intergalaktik/ulx4m-ld/pic/Blender_ULX4M-LD-003-full-ress.png

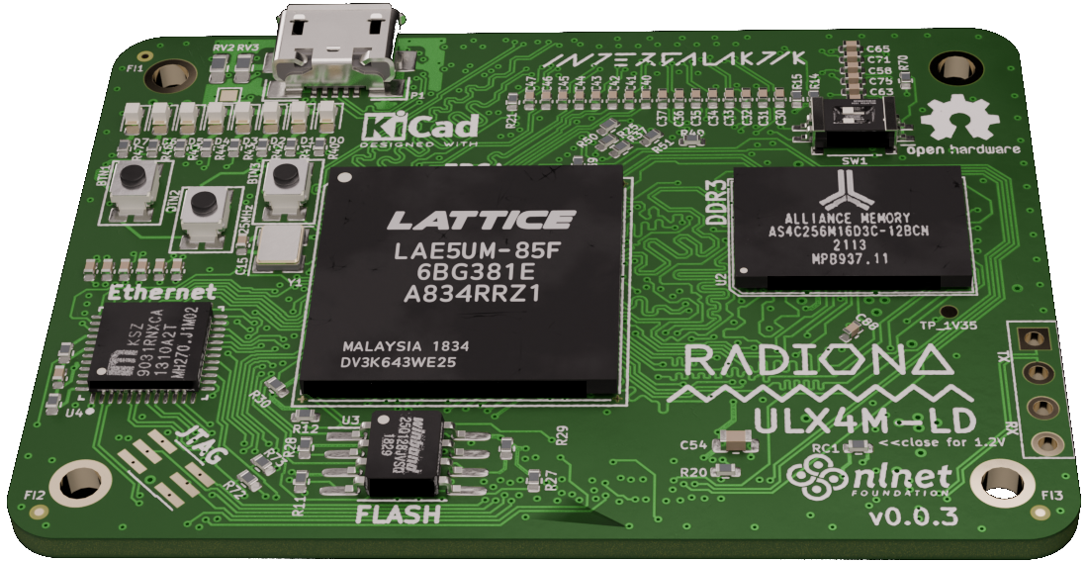
pic/Blender_ULX4M-LD-003-full-ress.png
