intergalaktik/ulx4m-ld/ddr3.kicad_sch

## KiCad design ddr3.kicad_sch (2025-04-05)

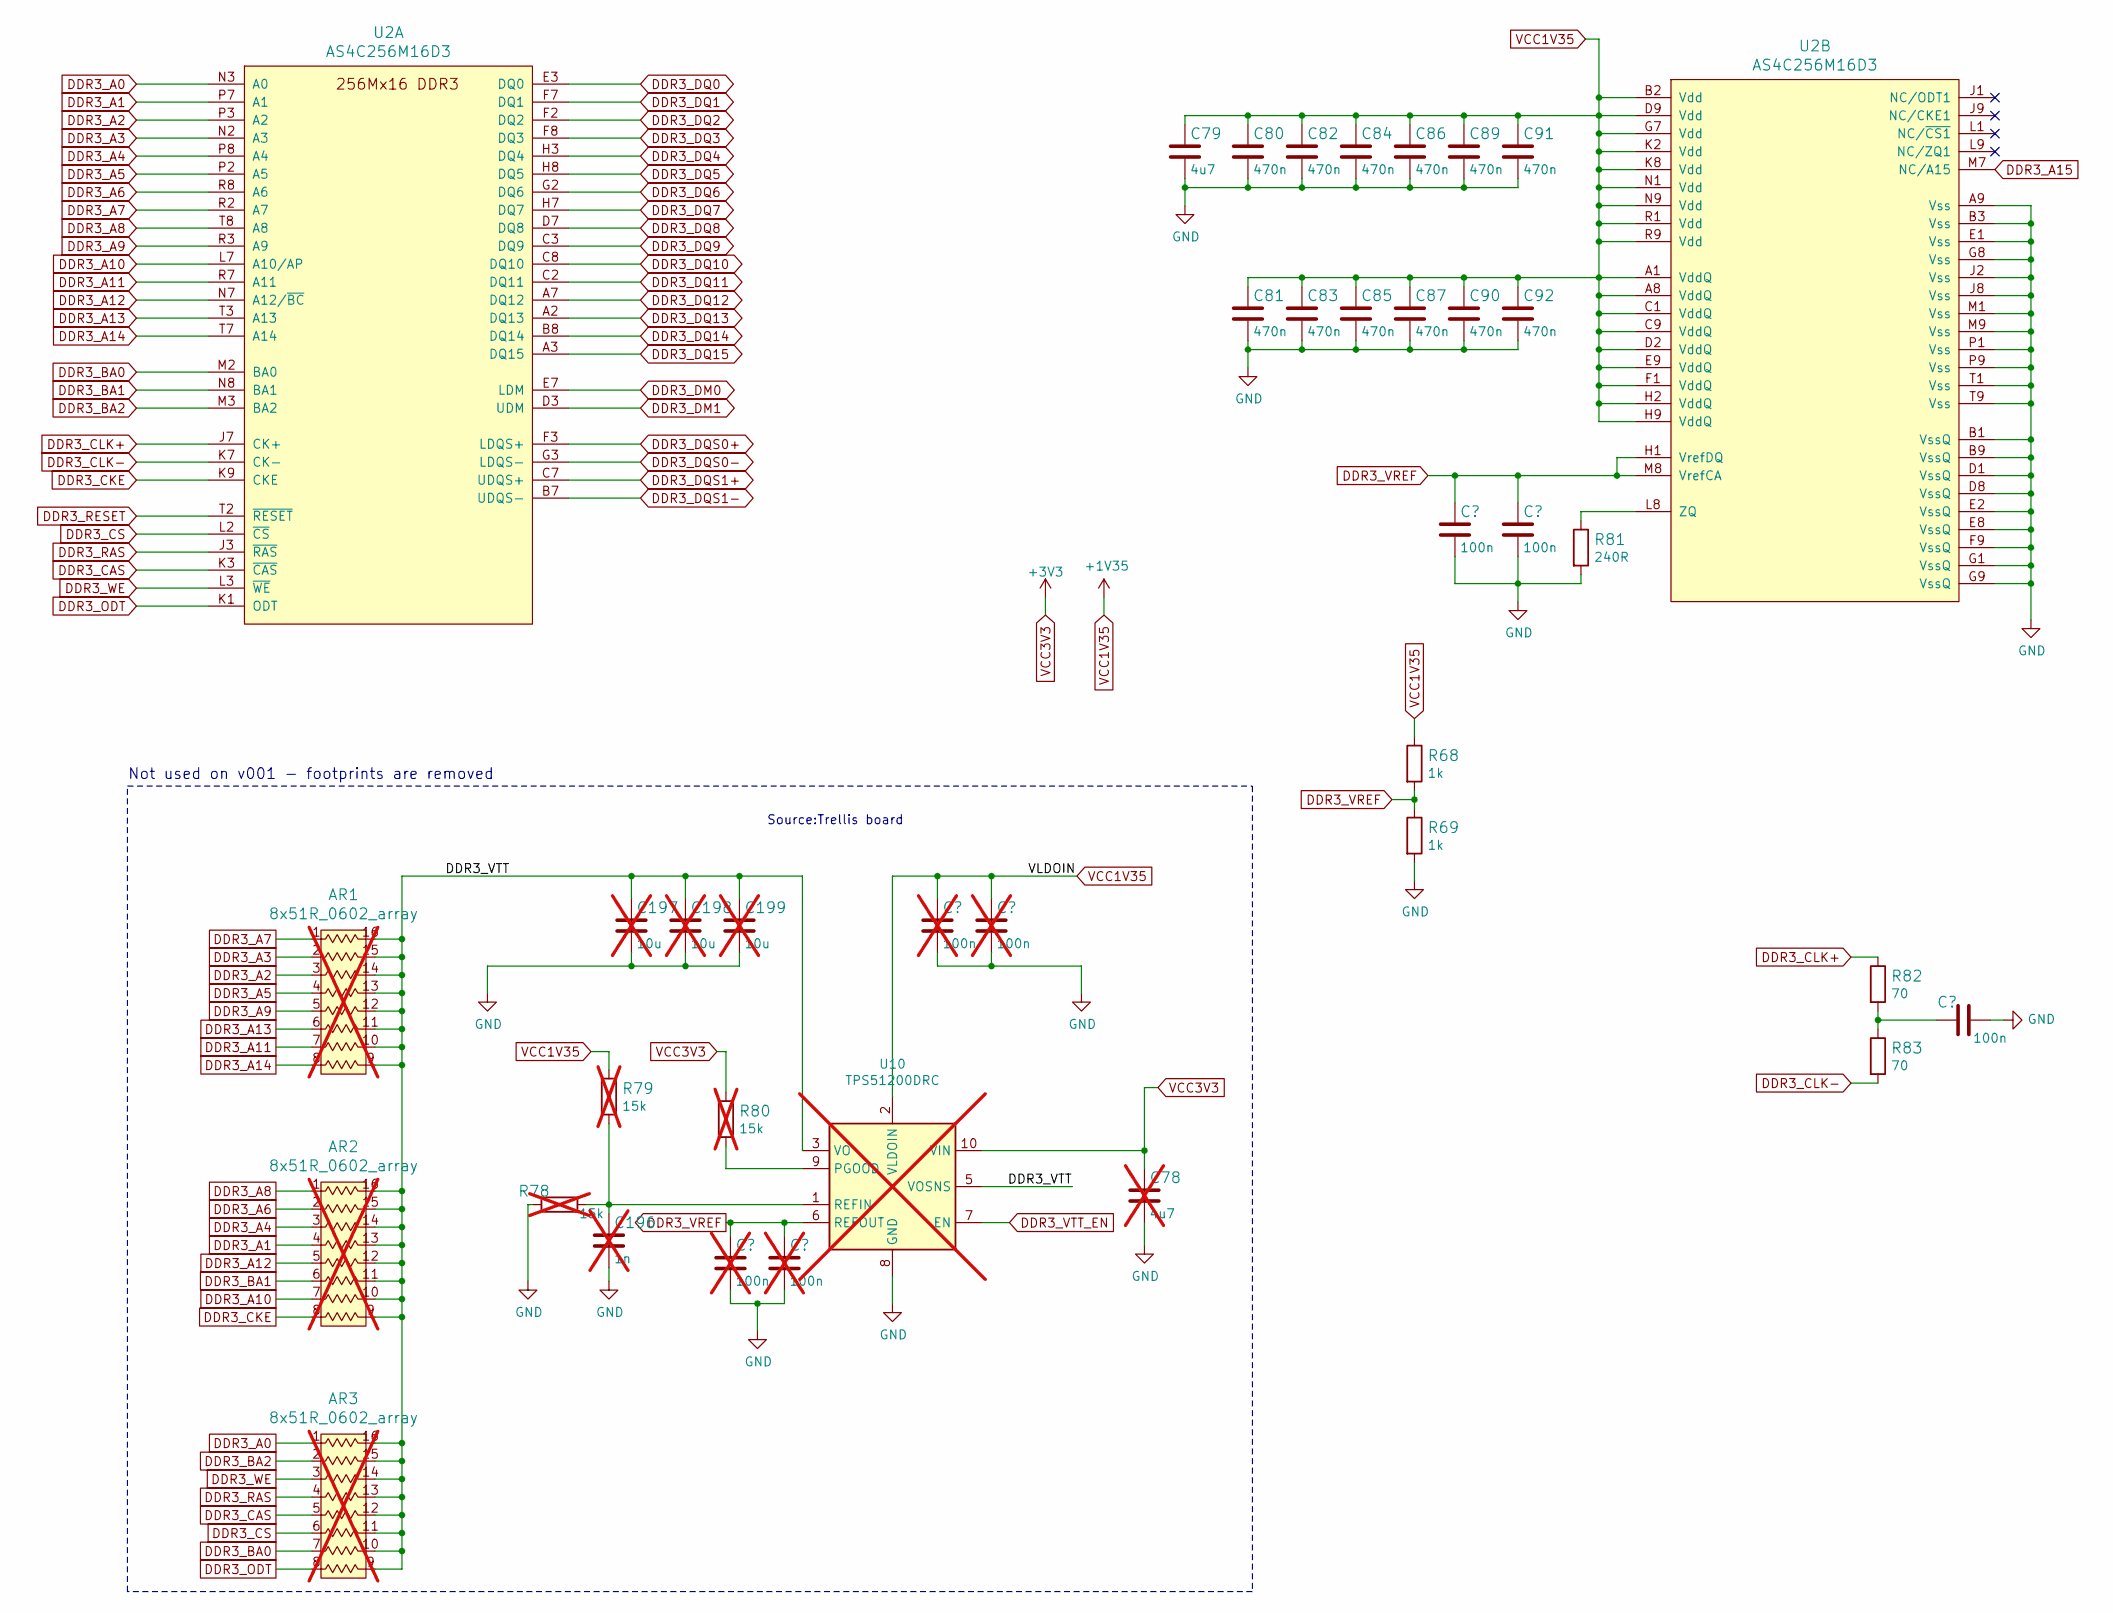
[picture p37: schematic ddr3.kicad_sch]

Parts:
AR1, AR2, AR3: 8x51R_0602_array; MPN EXB2HV510JV; not fitted
C78: 4u7; C_0402_1005Metric; MPN GRM155R60J106ME44D; not fitted
C79: 470n; C_0402_1005Metric; MPN GRM155R61A475MEAAD
C80, C81, C82, C83, C84, C85, C86, C87, C89, C90, C91, C92: 470n; C_0402_1005Metric; MPN C1005X5R1E474M050BB
C88, C93, C94: 100n; C_0402_1005Metric; MPN 0402X104K6R3CT
C196: 1n; MPN CC0402KRX7R9BB102; not fitted
C197, C198, C199: 10u; MPN GRM155R60J106ME44D; not fitted
C200, C201, C202, C240: 100n; MPN 0402X104K6R3CT; not fitted
R68, R69: 1k; R_0402_1005Metric; MPN CRCW040210K0FKEDHP
R78, R79, R80: 15k; MPN CRCW040210K0FKEDHP; not fitted
R81: 240R; R_0402_1005Metric; MPN ERJ2GEJ241X
R82, R83: 70; R_0402_1005Metric; MPN RC0402FR-0751RL
U2: AS4C256M16D3; BGA-96_9.0x13.0mm_Layout2x3x16_P0.8mm
U10: TPS51200DRC; not fitted

Connections:
+1V35: C79.1, C80.1, C81.1, C82.1, C83.1, C84.1, C85.1, C86.1, C87.1, C89.1, C90.1, C91.1, C92.1, C202.1, C240.1, R68.1, R79.1, U2.A1 (VddQ), U2.A8 (VddQ), U2.B2 (Vdd), U2.C1 (VddQ), U2.C9 (VddQ), U2.D2 (VddQ), U2.D9 (Vdd), U2.E9 (VddQ), U2.F1 (VddQ), U2.G7 (Vdd), U2.H2 (VddQ), U2.H9 (VddQ), U2.K2 (Vdd), U2.K8 (Vdd), U2.N1 (Vdd), U2.N9 (Vdd), U2.R1 (Vdd), U2.R9 (Vdd), U10.2 (VLDOIN)
+3V3: C78.1, R80.1, U10.10 (VIN)
DDR3_A0: AR3.1, U2.N3 (A0)
DDR3_A1: AR2.4, U2.P7 (A1)
DDR3_A2: AR1.3, U2.P3 (A2)
DDR3_A3: AR1.2, U2.N2 (A3)
DDR3_A4: AR2.3, U2.P8 (A4)
DDR3_A5: AR1.4, U2.P2 (A5)
DDR3_A6: AR2.2, U2.R8 (A6)
DDR3_A7: AR1.1, U2.R2 (A7)
DDR3_A8: AR2.1, U2.T8 (A8)
DDR3_A9: AR1.5, U2.R3 (A9)
DDR3_A10: AR2.7, U2.L7 (A10/AP)
DDR3_A11: AR1.7, U2.R7 (A11)
DDR3_A12: AR2.5, U2.N7 (A12/~BC)
DDR3_A13: AR1.6, U2.T3 (A13)
DDR3_A14: AR1.8, U2.T7 (A14)
DDR3_A15: U2.M7 (NC/A15)
DDR3_BA0: AR3.7, U2.M2 (BA0)
DDR3_BA1: AR2.6, U2.N8 (BA1)
DDR3_BA2: AR3.2, U2.M3 (BA2)
DDR3_CAS: AR3.5, U2.K3 (~CAS)
DDR3_CKE: AR2.8, U2.K9 (CKE)
DDR3_CLK+: R82.1, U2.J7 (CK+)
DDR3_CLK-: R83.2, U2.K7 (CK-)
DDR3_CS: AR3.6, U2.L2 (~CS)
DDR3_DM0: U2.E7 (LDM)
DDR3_DM1: U2.D3 (UDM)
DDR3_DQ0: U2.E3 (DQ0)
DDR3_DQ1: U2.F7 (DQ1)
DDR3_DQ2: U2.F2 (DQ2)
DDR3_DQ3: U2.F8 (DQ3)
DDR3_DQ4: U2.H3 (DQ4)
DDR3_DQ5: U2.H8 (DQ5)
DDR3_DQ6: U2.G2 (DQ6)
DDR3_DQ7: U2.H7 (DQ7)
DDR3_DQ8: U2.D7 (DQ8)
DDR3_DQ9: U2.C3 (DQ9)
DDR3_DQ10: U2.C8 (DQ10)
DDR3_DQ11: U2.C2 (DQ11)
DDR3_DQ12: U2.A7 (DQ12)
DDR3_DQ13: U2.A2 (DQ13)
DDR3_DQ14: U2.B8 (DQ14)
DDR3_DQ15: U2.A3 (DQ15)
DDR3_DQS0+: U2.F3 (LDQS+)
DDR3_DQS0-: U2.G3 (LDQS-)
DDR3_DQS1+: U2.C7 (UDQS+)
DDR3_DQS1-: U2.B7 (UDQS-)
DDR3_ODT: AR3.8, U2.K1 (ODT)
DDR3_RAS: AR3.4, U2.J3 (~RAS)
DDR3_RESET: U2.T2 (~RESET)
DDR3_VREF: C88.1, C93.1, C200.1, C201.1, R68.2, R69.1, U2.H1 (VrefDQ), U2.M8 (VrefCA), U10.6 (REFOUT)
DDR3_VTT: AR1.9, AR1.10, AR1.11, AR1.12, AR1.13, AR1.14, AR1.15, AR1.16, AR2.9, AR2.10, AR2.11, AR2.12, AR2.13, AR2.14, AR2.15, AR2.16, AR3.9, AR3.10, AR3.11, AR3.12, AR3.13, AR3.14, AR3.15, AR3.16, C197.1, C198.1, C199.1, U10.3 (VO), U10.5 (VOSNS)
DDR3_VTT_EN: U10.7 (EN)
DDR3_WE: AR3.3, U2.L3 (~WE)
GND: C78.2, C79.2, C80.2, C81.2, C82.2, C83.2, C84.2, C85.2, C86.2, C87.2, C88.2, C89.2, C90.2, C91.2, C92.2, C93.2, C94.1, C196.2, C197.2, C198.2, C199.2, C200.2, C201.2, C202.2, C240.2, R69.2, R78.2, R81.2, U2.A9 (Vss), U2.B1 (VssQ), U2.B3 (Vss), U2.B9 (VssQ), U2.D1 (VssQ), U2.D8 (VssQ), U2.E1 (Vss), U2.E2 (VssQ), U2.E8 (VssQ), U2.F9 (VssQ), U2.G1 (VssQ), U2.G8 (Vss), U2.G9 (VssQ), U2.J2 (Vss), U2.J8 (Vss), U2.M1 (Vss), U2.M9 (Vss), U2.P1 (Vss), U2.P9 (Vss), U2.T1 (Vss), U2.T9 (Vss), U10.4 (GND), U10.8 (GND), U10.11 (GND)
unnamed: C94.2, R82.2, R83.1
unnamed: C196.1, R78.1, R79.2, U10.1 (REFIN)
unnamed: R80.2, U10.9 (PGOOD)
unnamed: R81.1, U2.L8 (ZQ)

Notes on the sheet:
Not used on v001 - footprints are removed
Source:Trellis board
