intergalaktik/ulx4m-ld/ethernet.kicad_sch

## KiCad design ethernet.kicad_sch (2025-04-05)

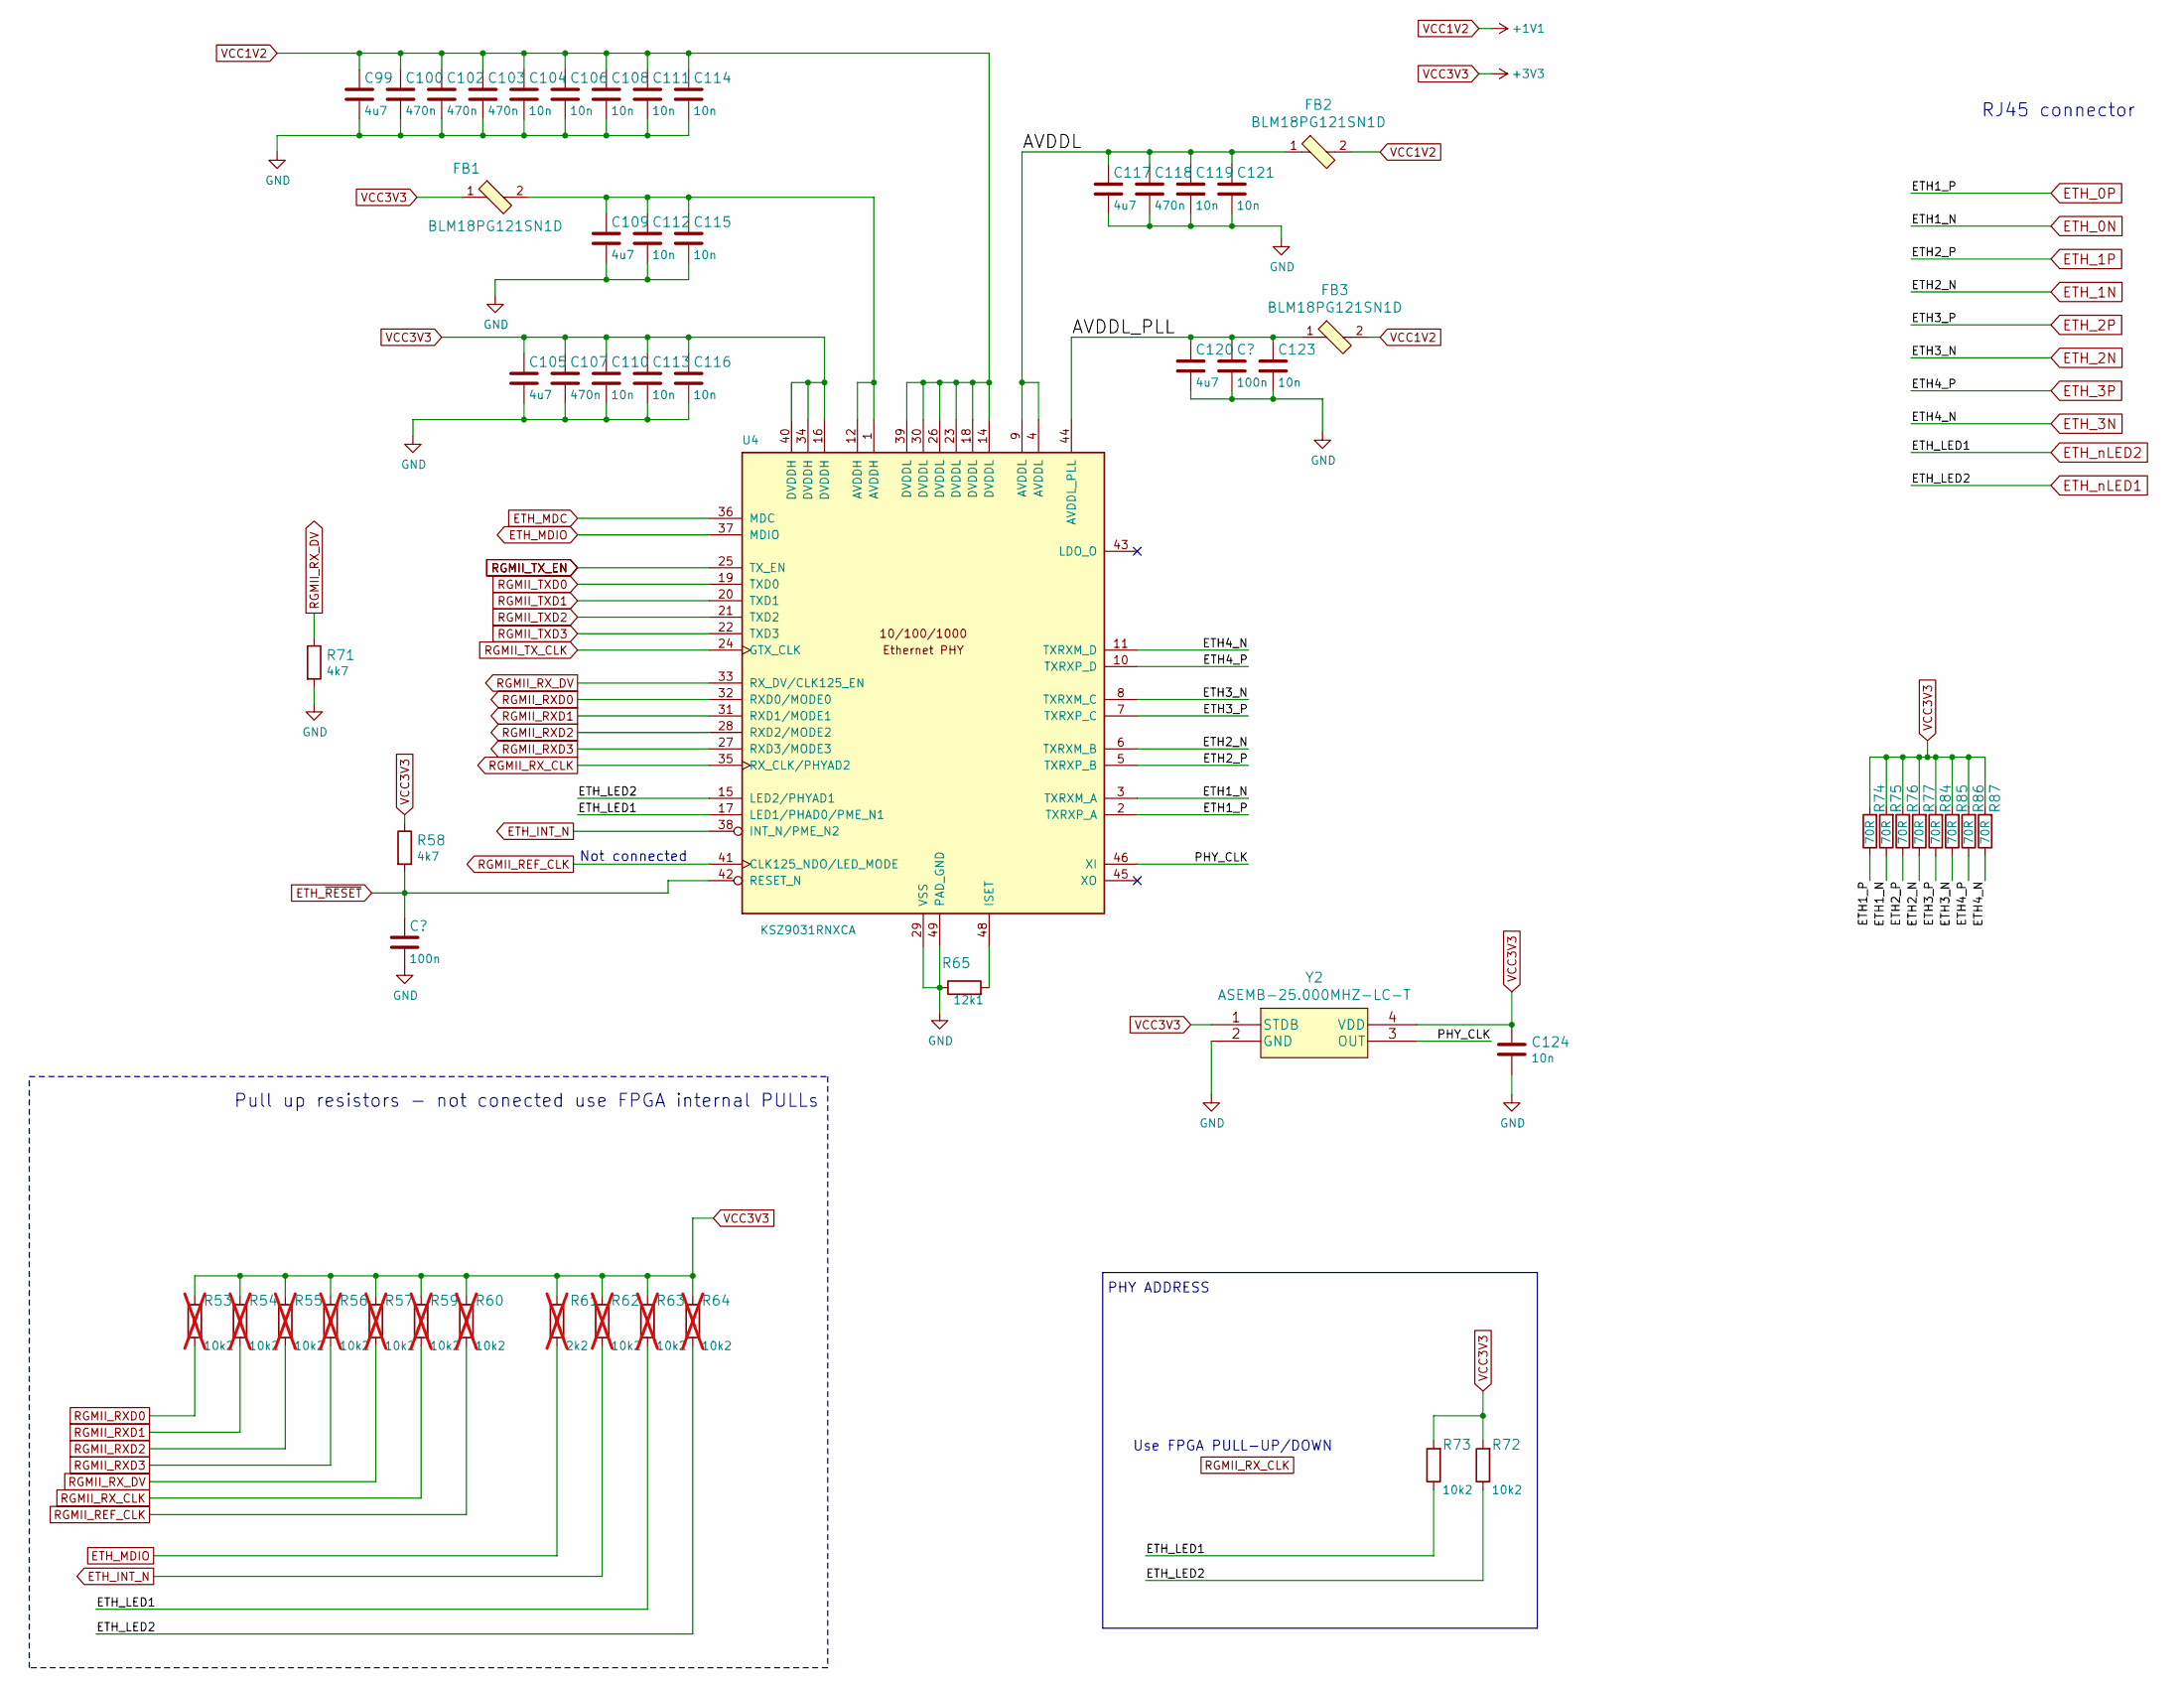
[picture p38: schematic ethernet.kicad_sch]

Parts:
C99, C105, C109, C117, C120: 4u7; C_0402_1005Metric; MPN GRM155R61A475MEAAD
C100, C102, C103, C107, C118: 470n; C_0402_1005Metric; MPN C1005X5R1E474M050BB
C101, C122: 100n; C_0402_1005Metric; MPN 0402X104K6R3CT
C104, C106, C108, C110, C111, C112, C113, C114, C115, C116, C119, C121, C123, C124: 10n; C_0402_1005Metric; MPN 04025G103ZAT2A
FB1, FB2, FB3: BLM18PG121SN1D; L_0603_1608Metric; MPN BLM18PG121SN1D
R53, R54, R55, R56, R57, R59, R60, R62, R63, R64: 10k2; MPN MCWR04X1022FTL; not fitted
R58, R71: 4k7; R_0402_1005Metric; MPN ERJ2GEJ472X
R61: 2k2; MPN RC0402FR-072K2L; not fitted
R65: 12k1; R_0402_1005Metric; MPN MCWR04X1212FTL
R72, R73, R74, R75, R76, R77, R84, R85, R86, R87: 10k2; R_0402_1005Metric; MPN MCWR04X1022FTL
U4: KSZ9031RNXCA; QFN-48-Microchip-QFN77-48LD-PL-2; MPN KSZ9031RNXCA
Y2: ASEMB-25.000MHZ-LC-T; OSC_ASEM1-16.000MHZ-LC-T

Connections:
+1V1: C99.1, C100.1, C102.1, C103.1, C104.1, C106.1, C108.1, C111.1, C114.1, FB2.2, FB3.2, U4.14 (DVDDL), U4.18 (DVDDL), U4.23 (DVDDL), U4.26 (DVDDL), U4.30 (DVDDL), U4.39 (DVDDL)
+3V3: C105.1, C107.1, C110.1, C113.1, C116.1, C124.1, FB1.1, R53.2, R54.2, R55.2, R56.2, R57.2, R58.1, R59.2, R60.2, R61.1, R62.2, R63.2, R64.2, R72.2, R73.2, R74.2, R75.2, R76.2, R77.2, R84.2, R85.2, R86.2, R87.2, U4.16 (DVDDH), U4.34 (DVDDH), U4.40 (DVDDH), Y2.1 (STDB), Y2.4 (VDD)
AVDDL: C117.1, C118.1, C119.1, C121.1, FB2.1, U4.4 (AVDDL), U4.9 (AVDDL)
AVDDL_PLL: C120.1, C122.1, C123.1, FB3.1, U4.44 (AVDDL_PLL)
ETH_0N: R75.1, U4.3 (TXRXM_A)
ETH_0P: R74.1, U4.2 (TXRXP_A)
ETH_1N: R77.1, U4.6 (TXRXM_B)
ETH_1P: R76.1, U4.5 (TXRXP_B)
ETH_2N: R85.1, U4.8 (TXRXM_C)
ETH_2P: R84.1, U4.7 (TXRXP_C)
ETH_3N: R87.1, U4.11 (TXRXM_D)
ETH_3P: R86.1, U4.10 (TXRXP_D)
ETH_INT_N: R62.1, U4.38 (INT_N/PME_N2)
ETH_MDC: U4.36 (MDC)
ETH_MDIO: R61.2, U4.37 (MDIO)
ETH_nLED1: R64.1, R72.1, U4.15 (LED2/PHYAD1)
ETH_nLED2: R63.1, R73.1, U4.17 (LED1/PHAD0/PME_N1)
ETH_~RESET: C101.1, R58.2, U4.42 (RESET_N)
GND: C99.2, C100.2, C101.2, C102.2, C103.2, C104.2, C105.2, C106.2, C107.2, C108.2, C109.2, C110.2, C111.2, C112.2, C113.2, C114.2, C115.2, C116.2, C117.2, C118.2, C119.2, C120.2, C121.2, C122.2, C123.2, C124.2, R65.1, R71.2, U4.29 (VSS), U4.49 (PAD_GND), Y2.2 (GND)
unnamed: C109.1, C112.1, C115.1, FB1.2, U4.1 (AVDDH), U4.12 (AVDDH)
unnamed: R65.2, U4.48 (ISET)
PHY_CLK: U4.46 (XI), Y2.3 (OUT)
RGMII_REF_CLK: R60.1, U4.41 (CLK125_NDO/LED_MODE)
RGMII_RXD0: R53.1, U4.32 (RXD0/MODE0)
RGMII_RXD1: R54.1, U4.31 (RXD1/MODE1)
RGMII_RXD2: R55.1, U4.28 (RXD2/MODE2)
RGMII_RXD3: R56.1, U4.27 (RXD3/MODE3)
RGMII_RX_CLK: R59.1, U4.35 (RX_CLK/PHYAD2)
RGMII_RX_DV: R57.1, R71.1, U4.33 (RX_DV/CLK125_EN)
RGMII_TXD0: U4.19 (TXD0)
RGMII_TXD1: U4.20 (TXD1)
RGMII_TXD2: U4.21 (TXD2)
RGMII_TXD3: U4.22 (TXD3)
RGMII_TX_CLK: U4.24 (GTX_CLK)
RGMII_TX_EN: U4.25 (TX_EN)

Notes on the sheet:
Pull up resistors - not conected use FPGA internal PULLs
PHY ADDRESS
RJ45 connector
Not connected
Use FPGA PULL-UP/DOWN
