intergalaktik/ulx4m-ld/gpio.kicad_sch

## KiCad design gpio.kicad_sch (2025-04-05)

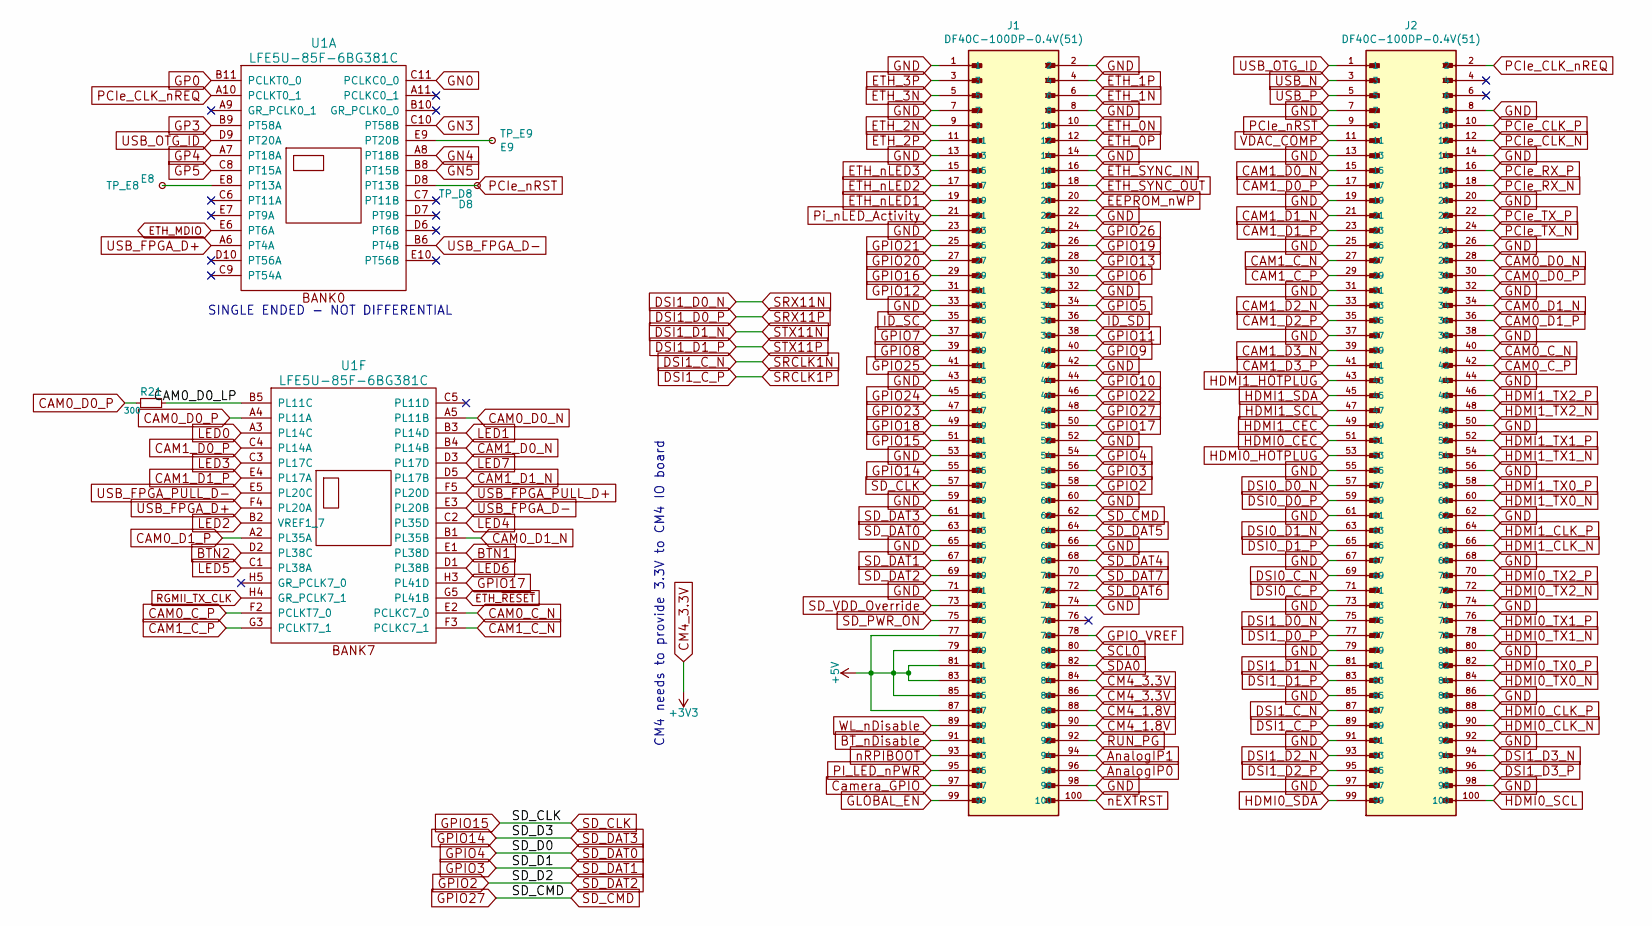
[picture p41: schematic gpio.kicad_sch]

Parts:
J1, J2: DF40C-100DP-0.4V(51); HRS_DF40C-100DP-0.4V(51); PARTREV 02/2020
R21: 300; R_0402_1005Metric
TP_D8: D8; Testpoint_smd_1mm
TP_E8: E8; Testpoint_smd_1mm
TP_E9: E9; Testpoint_smd_1mm
U1: LFE5U-85F-6BG381C; BGA-381_pitch0.8mm_dia0.4mm; MPN LFE5U-85F-6BG381C

Connections:
+3V3: J1.84, J1.86
+5V: J1.77, J1.79, J1.81, J1.83, J1.85, J1.87
AnalogIP0: J1.96
AnalogIP1: J1.94
BTN1: U1.E1 (PL38D)
BTN2: U1.D2 (PL38C)
BT_nDisable: J1.91
CAM0_C_N: J2.40, U1.E2 (PCLKC7_0)
CAM0_C_P: J2.42, U1.F2 (PCLKT7_0)
CAM0_D0_LP: R21.2, U1.B5 (PL11C)
CAM0_D0_N: J2.28, U1.A5 (PL11B)
CAM0_D0_P: J2.30, R21.1, U1.A4 (PL11A)
CAM0_D1_N: J2.34, U1.B1 (PL35B)
CAM0_D1_P: J2.36, U1.A2 (PL35A)
CAM1_C_N: J2.27, U1.F3 (PCLKC7_1)
CAM1_C_P: J2.29, U1.G3 (PCLKT7_1)
CAM1_D0_N: J2.15, U1.B4 (PL14B)
CAM1_D0_P: J2.17, U1.C4 (PL14A)
CAM1_D1_N: J2.21, U1.D5 (PL17B)
CAM1_D1_P: J2.23, U1.E4 (PL17A)
CAM1_D2_N: J2.33
CAM1_D2_P: J2.35
CAM1_D3_N: J2.39
CAM1_D3_P: J2.41
CM4_1.8V: J1.88, J1.90
Camera_GPIO: J1.97
DSI0_C_N: J2.69
DSI0_C_P: J2.71
DSI0_D0_N: J2.57
DSI0_D0_P: J2.59
DSI0_D1_N: J2.63
DSI0_D1_P: J2.65
DSI1_C_N: J2.87
DSI1_C_P: J2.89
DSI1_D0_N: J2.75
DSI1_D0_P: J2.77
DSI1_D1_N: J2.81
DSI1_D1_P: J2.83
DSI1_D2_N: J2.93
DSI1_D2_P: J2.95
DSI1_D3_N: J2.94
DSI1_D3_P: J2.96
EEPROM_nWP: J1.20
ETH_0N: J1.10
ETH_0P: J1.12
ETH_1N: J1.6
ETH_1P: J1.4
ETH_2N: J1.9
ETH_2P: J1.11
ETH_3N: J1.5
ETH_3P: J1.3
ETH_MDIO: U1.E6 (PT6A)
ETH_SYNC_IN: J1.16
ETH_SYNC_OUT: J1.18
ETH_nLED1: J1.19
ETH_nLED2: J1.17
ETH_nLED3: J1.15
ETH_~RESET: U1.G5 (PL41B)
GLOBAL_EN: J1.99
GN0: U1.C11 (PCLKC0_0)
GN3: U1.C10 (PT58B)
GN4: U1.A8 (PT18B)
GN5: U1.B8 (PT15B)
GND: J1.1, J1.2, J1.7, J1.8, J1.13, J1.14, J1.22, J1.23, J1.32, J1.33, J1.42, J1.43, J1.52, J1.53, J1.59, J1.60, J1.65, J1.66, J1.71, J1.74, J1.98, J2.7, J2.8, J2.13, J2.14, J2.19, J2.20, J2.25, J2.26, J2.31, J2.32, J2.37, J2.38, J2.44, J2.50, J2.55, J2.56, J2.61, J2.62, J2.67, J2.68, J2.73, J2.74, J2.79, J2.80, J2.85, J2.86, J2.91, J2.92, J2.97, J2.98
GP0: U1.B11 (PCLKT0_0)
GP3: U1.B9 (PT58A)
GP4: U1.A7 (PT18A)
GP5: U1.C8 (PT15A)
GPIO2: J1.58, J1.69
GPIO3: J1.56, J1.67
GPIO4: J1.54, J1.63
GPIO5: J1.34
GPIO6: J1.30
GPIO7: J1.37
GPIO8: J1.39
GPIO9: J1.40
GPIO10: J1.44
GPIO11: J1.38
GPIO12: J1.31
GPIO13: J1.28
GPIO14: J1.55, J1.61
GPIO15: J1.51, J1.57
GPIO16: J1.29
GPIO17: J1.50, U1.H3 (PL41D)
GPIO18: J1.49
GPIO19: J1.26
GPIO20: J1.27
GPIO21: J1.25
GPIO22: J1.46
GPIO23: J1.47
GPIO24: J1.45
GPIO25: J1.41
GPIO26: J1.24
GPIO27: J1.48, J1.62
GPIO_VREF: J1.78
HDMI0_CEC: J2.51
HDMI0_CLK_N: J2.90
HDMI0_CLK_P: J2.88
HDMI0_HOTPLUG: J2.53
HDMI0_SCL: J2.100
HDMI0_SDA: J2.99
HDMI0_TX0_N: J2.84
HDMI0_TX0_P: J2.82
HDMI0_TX1_N: J2.78
HDMI0_TX1_P: J2.76
HDMI0_TX2_N: J2.72
HDMI0_TX2_P: J2.70
HDMI1_CEC: J2.49
HDMI1_CLK_N: J2.66
HDMI1_CLK_P: J2.64
HDMI1_HOTPLUG: J2.43
HDMI1_SCL: J2.47
HDMI1_SDA: J2.45
HDMI1_TX0_N: J2.60
HDMI1_TX0_P: J2.58
HDMI1_TX1_N: J2.54
HDMI1_TX1_P: J2.52
HDMI1_TX2_N: J2.48
HDMI1_TX2_P: J2.46
ID_SC: J1.35
ID_SD: J1.36
LED0: U1.A3 (PL14C)
LED1: U1.B3 (PL14D)
LED2: U1.B2 (VREF1_7)
LED3: U1.C3 (PL17C)
LED4: U1.C2 (PL35D)
LED5: U1.C1 (PL38A)
LED6: U1.D1 (PL38B)
LED7: U1.D3 (PL17D)
unnamed: TP_E8.1, U1.E8 (PT13A)
unnamed: TP_E9.1, U1.E9 (PT20B)
PCIe_CLK_N: J2.12
PCIe_CLK_P: J2.10
PCIe_CLK_nREQ: J2.2, U1.A10 (PCLKT0_1)
PCIe_RX_N: J2.18
PCIe_RX_P: J2.16
PCIe_TX_N: J2.24
PCIe_TX_P: J2.22
PCIe_nRST: J2.9, TP_D8.1, U1.D8 (PT13B)
PI_LED_nPWR: J1.95
Pi_nLED_Activity: J1.21
RGMII_TX_CLK: U1.H4 (GR_PCLK7_1)
RUN_PG: J1.92
SCL0: J1.80
SDA0: J1.82
SD_DAT4: J1.68
SD_DAT5: J1.64
SD_DAT6: J1.72
SD_DAT7: J1.70
SD_PWR_ON: J1.75
SD_VDD_Override: J1.73
USB_FPGA_D+: U1.A6 (PT4A), U1.F4 (PL20A)
USB_FPGA_D-: U1.B6 (PT4B), U1.E3 (PL20B)
USB_FPGA_PULL_D+: U1.F5 (PL20D)
USB_FPGA_PULL_D-: U1.E5 (PL20C)
USB_N: J2.3
USB_OTG_ID: J2.1, U1.D9 (PT20A)
USB_P: J2.5
VDAC_COMP: J2.11
WL_nDisable: J1.89
nEXTRST: J1.100
nRPIBOOT: J1.93

Notes on the sheet:
CM4 needs to provide 3.3V to CM4 IO board
SINGLE ENDED - NOT DIFFERENTIAL
