intergalaktik/ulx4m-ld/power.kicad_sch

## KiCad design power.kicad_sch (2025-04-09)

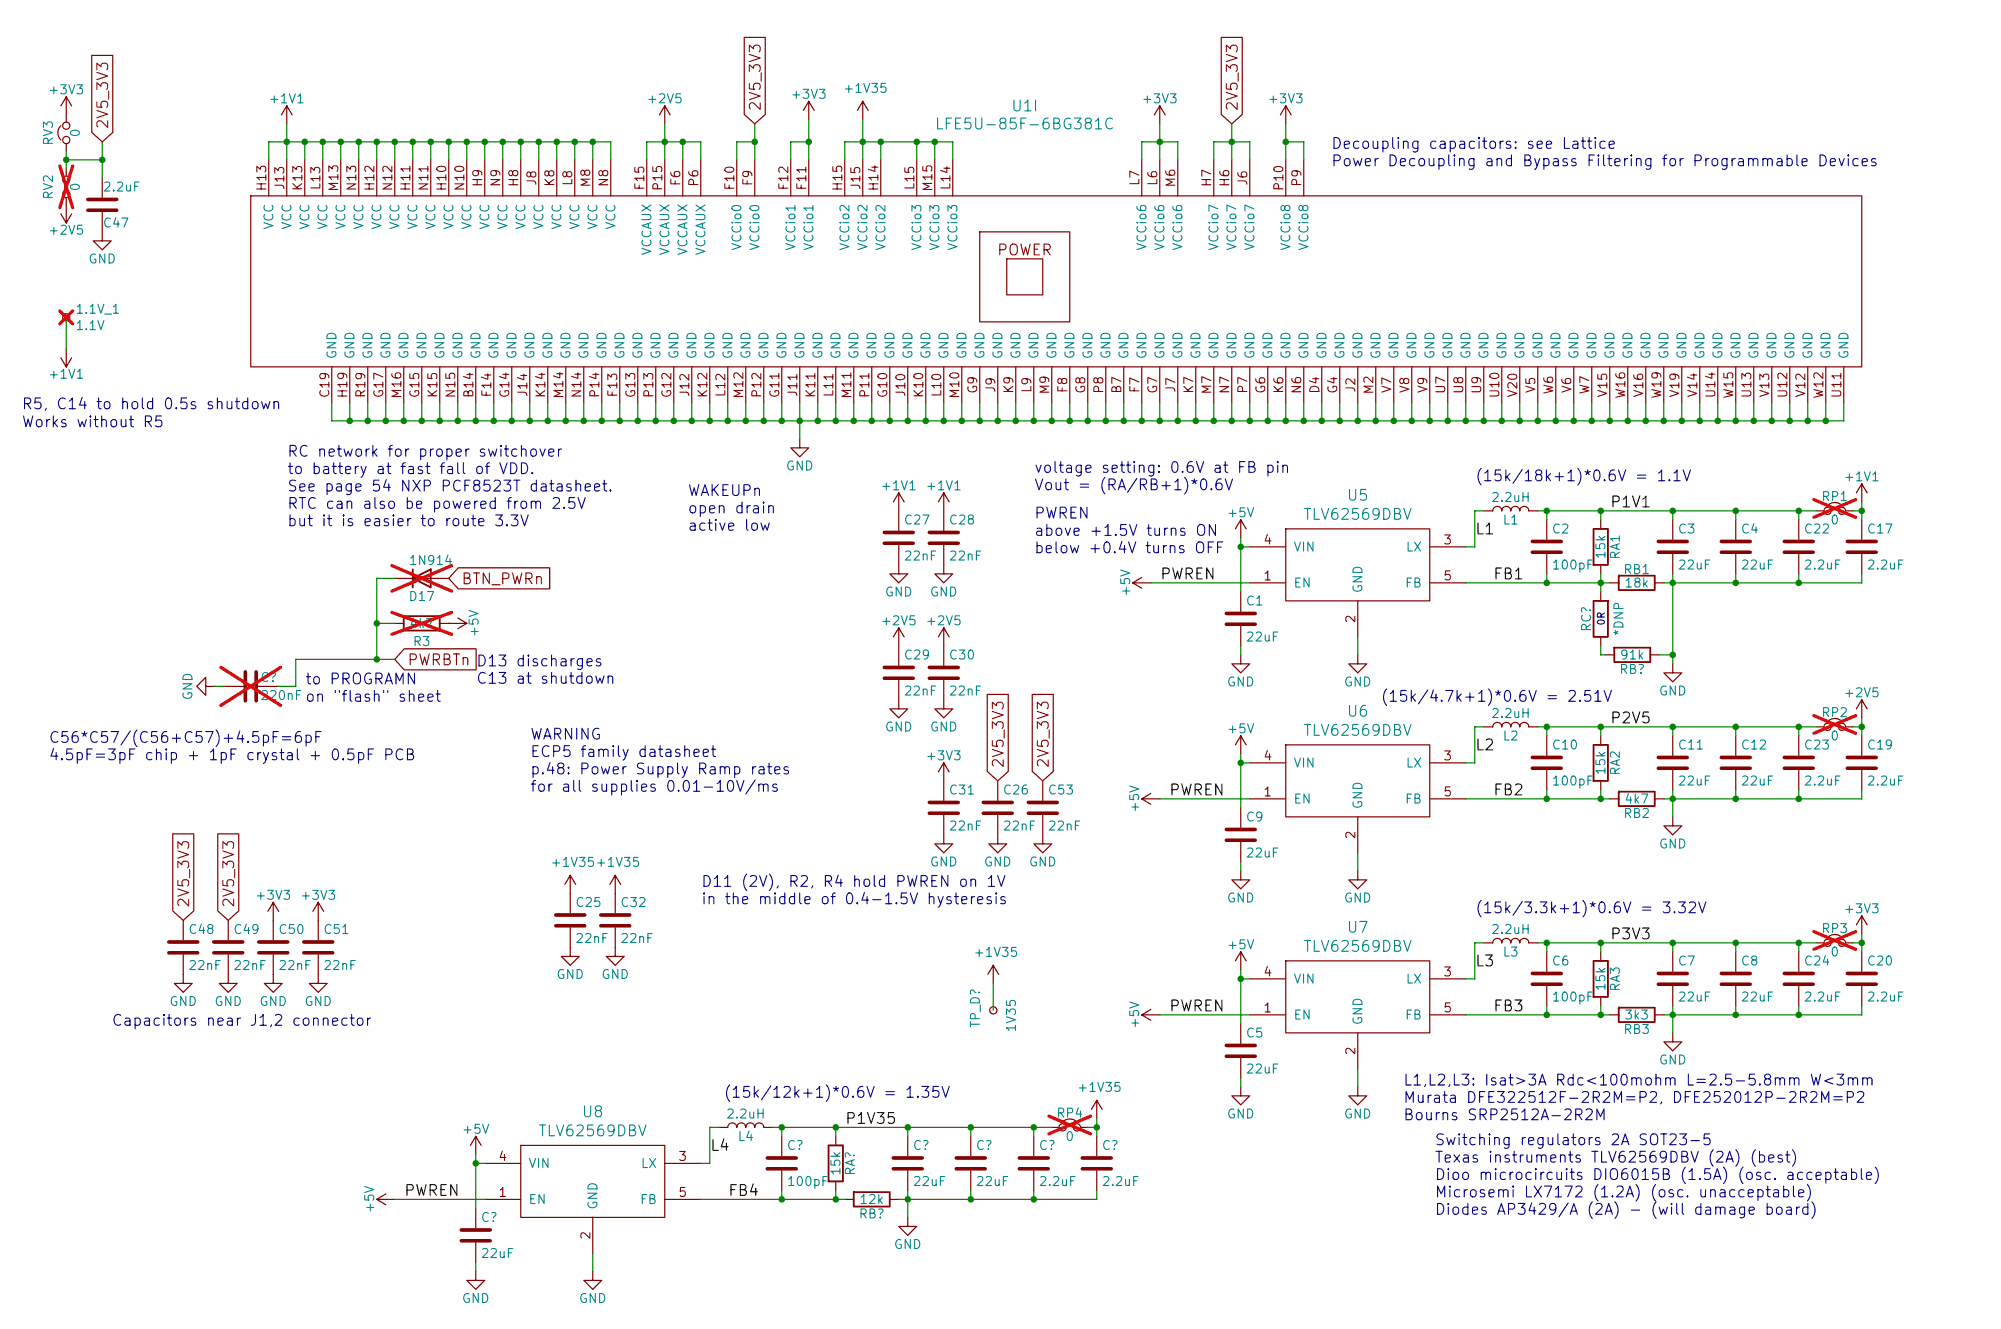
[picture p42: schematic power.kicad_sch]

Parts:
1.1V_1: 1.1V; TestPoint_Pad_1.0x1.0mm; not fitted
C1: 22uF; C_0603_1608Metric; MPN CC0805ZKY5V5BB226; Mouser 81-GRM21BR61A226ME1L
C2: 100pF; C_0402_1005Metric; MPN CS0603KRX7R9BB471; Mouser 581-06035A101JAT4A
C3, C4, C7, C8, C11, C12, C95, C96: 22uF; C_0603_1608Metric
C5, C9, C76: 22uF; C_0603_1608Metric; MPN CC0805ZKY5V5BB226
C6, C10, C77: 100pF; C_0402_1005Metric
C17, C19, C20, C22, C23, C24, C97, C98: 2.2uF; C_0603_1608Metric
C25: 22nF; C_0402_1005Metric; MPN CC0603JRX7R8BB223; Mouser 603-CC603KRX7R7BB223
C26, C27, C28, C29, C30, C31, C32: 22nF; C_0402_1005Metric; MPN CX0603MRX7R8BB223
C47: 2.2uF; C_0603_1608Metric; MPN CC0805MRX5R6BB225
C48, C49, C50, C51, C53: 22nF; C_0603_1608Metric; MPN CX0603MRX7R8BB223
C60: 220nF; not fitted
D17: 1N914; not fitted
L1: 2.2uH; L_1008_1210; MPN DFE322512F-2R2M=P2; Mouser 81-DFE322512F-2R2MP2
L2, L3, L4: 2.2uH; L_1008_1210
R3: 4k7; MPN AC0603FR-104K7L; not fitted
RA1: 15k; R_0402_1005Metric; MPN RC0603FR-1015KL
RA2, RA3, RA4: 15k; R_0402_1005Metric
RB1: 18k; R_0402_1005Metric; MPN RC0603FR-1018KL; Mouser 71-CRCW060318K0FKEAC
RB2: 4k7; R_0402_1005Metric; MPN AC0603FR-104K7L
RB3: 3k3; R_0402_1005Metric; MPN RT0603FRE073K3L; Mouser 603-RC0603FR-073K3L
RB4: 12k; R_0402_1005Metric; MPN RT0603FRE073K3L; Mouser 603-RC0603FR-073K3L
RC1: *DNP; R_0402_1005Metric; MPN RC0603FR-1018KL; Mouser 71-CRCW060318K0FKEAC
RC2: 91k; R_0402_1005Metric; MPN RC0603FR-1018KL; Mouser 71-CRCW060318K0FKEAC
RP1: 0; R_0805_2012Metric_Pad1.29x1.40mm_HandSolder_Jumper_NC; Mouser_URL www.mouser.com; not fitted
RP2, RP3, RP4: 0; R_0805_2012Metric_Pad1.29x1.40mm_HandSolder_Jumper_NC; not fitted
RV2: 0; R_0603_1608Metric_Pad0.98x0.95mm_HandSolder; not fitted
RV3: 0; R_0603_1608Metric_Pad0.98x0.95mm_HandSolder; MPN RC0805JR-070RL; Mouser 71-RCG08050000Z0EA
TP_1V35: 1V35; Testpoint_smd_1mm
U1: LFE5U-85F-6BG381C; BGA-381_pitch0.8mm_dia0.4mm; MPN LFE5U-85F-6BG381C
U5: TLV62569DBV; TSOT-25; MPN TLV62569DBVR; Mouser 595-TLV62569DBVT
U6, U7, U8: TLV62569DBV; TSOT-25; MPN TLV62569DBVR; Mouser 595-TLV62569DBVR

Connections:
2V5_3V3: C26.1, C47.1, C48.1, C49.1, C53.1, RV2.2, RV3.1, U1.F9 (VCCio0), U1.F10 (VCCio0), U1.H6 (VCCio7), U1.H7 (VCCio7), U1.J6 (VCCio7)
+1V1: 1.1V_1.1, C17.1, C27.1, C28.1, RP1.2, U1.H8 (VCC), U1.H9 (VCC), U1.H10 (VCC), U1.H11 (VCC), U1.H12 (VCC), U1.H13 (VCC), U1.J8 (VCC), U1.J13 (VCC), U1.K8 (VCC), U1.K13 (VCC), U1.L8 (VCC), U1.L13 (VCC), U1.M8 (VCC), U1.M13 (VCC), U1.N8 (VCC), U1.N9 (VCC), U1.N10 (VCC), U1.N11 (VCC), U1.N12 (VCC), U1.N13 (VCC)
+1V35: C25.1, C32.1, C98.1, RP4.2, TP_1V35.1, U1.H14 (VCCio2), U1.H15 (VCCio2), U1.J15 (VCCio2), U1.L14 (VCCio3), U1.L15 (VCCio3), U1.M15 (VCCio3)
+2V5: C19.1, C29.1, C30.1, RP2.2, RV2.1, U1.F6 (VCCAUX), U1.F15 (VCCAUX), U1.P6 (VCCAUX), U1.P15 (VCCAUX)
+3V3: C20.1, C31.1, C50.1, C51.1, RP3.2, RV3.2, U1.F11 (VCCio1), U1.F12 (VCCio1), U1.L6 (VCCio6), U1.L7 (VCCio6), U1.M6 (VCCio6), U1.P9 (VCCio8), U1.P10 (VCCio8)
+5V: C1.1, C5.1, C9.1, C76.1, R3.1, U5.1 (EN), U5.4 (VIN), U6.1 (EN), U6.4 (VIN), U7.1 (EN), U7.4 (VIN), U8.1 (EN), U8.4 (VIN)
BTN_PWRn: D17.2 (A)
FB1: C2.2, RA1.2, RB1.2, RC1.2, U5.5 (FB)
FB2: C10.2, RA2.2, RB2.2, U6.5 (FB)
FB3: C6.2, RA3.2, RB3.2, U7.5 (FB)
FB4: C77.2, RA4.2, RB4.2, U8.5 (FB)
GND: C1.2, C3.2, C4.2, C5.2, C7.2, C8.2, C9.2, C11.2, C12.2, C17.2, C19.2, C20.2, C22.2, C23.2, C24.2, C25.2, C26.2, C27.2, C28.2, C29.2, C30.2, C31.2, C32.2, C47.2, C48.2, C49.2, C50.2, C51.2, C53.2, C60.2, C76.2, C95.2, C96.2, C97.2, C98.2, RB1.1, RB2.1, RB3.1, RB4.1, RC2.1, U1.B7 (GND), U1.B14 (GND), U1.C19 (GND), U1.D4 (GND), U1.F7 (GND), U1.F8 (GND), U1.F13 (GND), U1.F14 (GND), U1.G4 (GND), U1.G6 (GND), U1.G7 (GND), U1.G8 (GND), U1.G9 (GND), U1.G10 (GND), U1.G11 (GND), U1.G12 (GND), U1.G13 (GND), U1.G14 (GND), U1.G15 (GND), U1.G17 (GND), U1.H19 (GND), U1.J2 (GND), U1.J7 (GND), U1.J9 (GND), U1.J10 (GND), U1.J11 (GND), U1.J12 (GND), U1.J14 (GND), U1.K6 (GND), U1.K7 (GND), U1.K9 (GND), U1.K10 (GND), U1.K11 (GND), U1.K12 (GND), U1.K14 (GND), U1.K15 (GND), U1.L9 (GND), U1.L10 (GND), U1.L11 (GND), U1.L12 (GND), U1.M2 (GND), U1.M7 (GND), U1.M9 (GND), U1.M10 (GND), U1.M11 (GND), U1.M12 (GND), U1.M14 (GND), U1.M16 (GND), U1.N6 (GND), U1.N7 (GND), U1.N14 (GND), U1.N15 (GND), U1.P7 (GND), U1.P8 (GND), U1.P11 (GND), U1.P12 (GND), U1.P13 (GND), U1.P14 (GND), U1.R19 (GND), U1.U7 (GND), U1.U8 (GND), U1.U9 (GND), U1.U10 (GND), U1.U11 (GND), U1.U12 (GND), U1.U13 (GND), U1.U14 (GND), U1.V5 (GND), U1.V6 (GND), U1.V7 (GND), U1.V8 (GND), U1.V9 (GND), U1.V12 (GND), U1.V13 (GND), U1.V14 (GND), U1.V15 (GND), U1.V16 (GND), U1.V19 (GND), U1.V20 (GND), U1.W6 (GND), U1.W7 (GND), U1.W12 (GND), U1.W15 (GND), U1.W16 (GND), U1.W19 (GND), U5.2 (GND), U6.2 (GND), U7.2 (GND), U8.2 (GND)
L1: L1.1, U5.3 (LX)
L2: L2.1, U6.3 (LX)
L3: L3.1, U7.3 (LX)
L4: L4.1, U8.3 (LX)
unnamed: RC1.1, RC2.2
P1V1: C2.1, C3.1, C4.1, C22.1, L1.2, RA1.1, RP1.1
P1V35: C77.1, C95.1, C96.1, C97.1, L4.2, RA4.1, RP4.1
P2V5: C10.1, C11.1, C12.1, C23.1, L2.2, RA2.1, RP2.1
P3V3: C6.1, C7.1, C8.1, C24.1, L3.2, RA3.1, RP3.1
PWRBTn: C60.1, D17.1 (K), R3.2

Notes on the sheet:
WAKEUPn open drain active low
(15k/4.7k+1)*0.6V = 2.51V
L1,L2,L3: Isat>3A Rdc<100mohm L=2.5-5.8mm W<3mm Murata DFE322512F-2R2M=P2, DFE252012P-2R2M=P2 Bourns SRP2512A-2R2M
C56*C57/(C56+C57)+4.5pF=6pF 4.5pF=3pF chip + 1pF crystal + 0.5pF PCB
(15k/18k+1)*0.6V = 1.1V
R5, C14 to hold 0.5s shutdown
PWREN above +1.5V turns ON below +0.4V turns OFF
Capacitors near J1,2 connector
D13 discharges C13 at shutdown
voltage setting: 0.6V at FB pin Vout = (RA/RB+1)*0.6V
D11 (2V), R2, R4 hold PWREN on 1V in the middle of 0.4-1.5V hysteresis
WARNING ECP5 family datasheet p.48: Power Supply Ramp rates for all supplies 0.01-10V/ms
Works without R5
(15k/12k+1)*0.6V = 1.35V
Switching regulators 2A SOT23-5 Texas instruments TLV62569DBV (2A) (best) Dioo microcircuits DIO6015B (1.5A) (osc. acceptable) Microsemi LX7172 (1.2A) (osc. unacceptable) Diodes AP3429/A (2A) - (will damage board)
(15k/3.3k+1)*0.6V = 3.32V
RC network for proper switchover to battery at fast fall of VDD. See page 54 NXP PCF8523T datasheet. RTC can also be powered from 2.5V but it is easier to route 3.3V
to PROGRAMN on "flash" sheet
Decoupling capacitors: see Lattice Power Decoupling and Bypass Filtering for Programmable Devices
