intergalaktik/ulx4m-ld/ram.kicad_sch

## KiCad design ram.kicad_sch (2025-04-05)

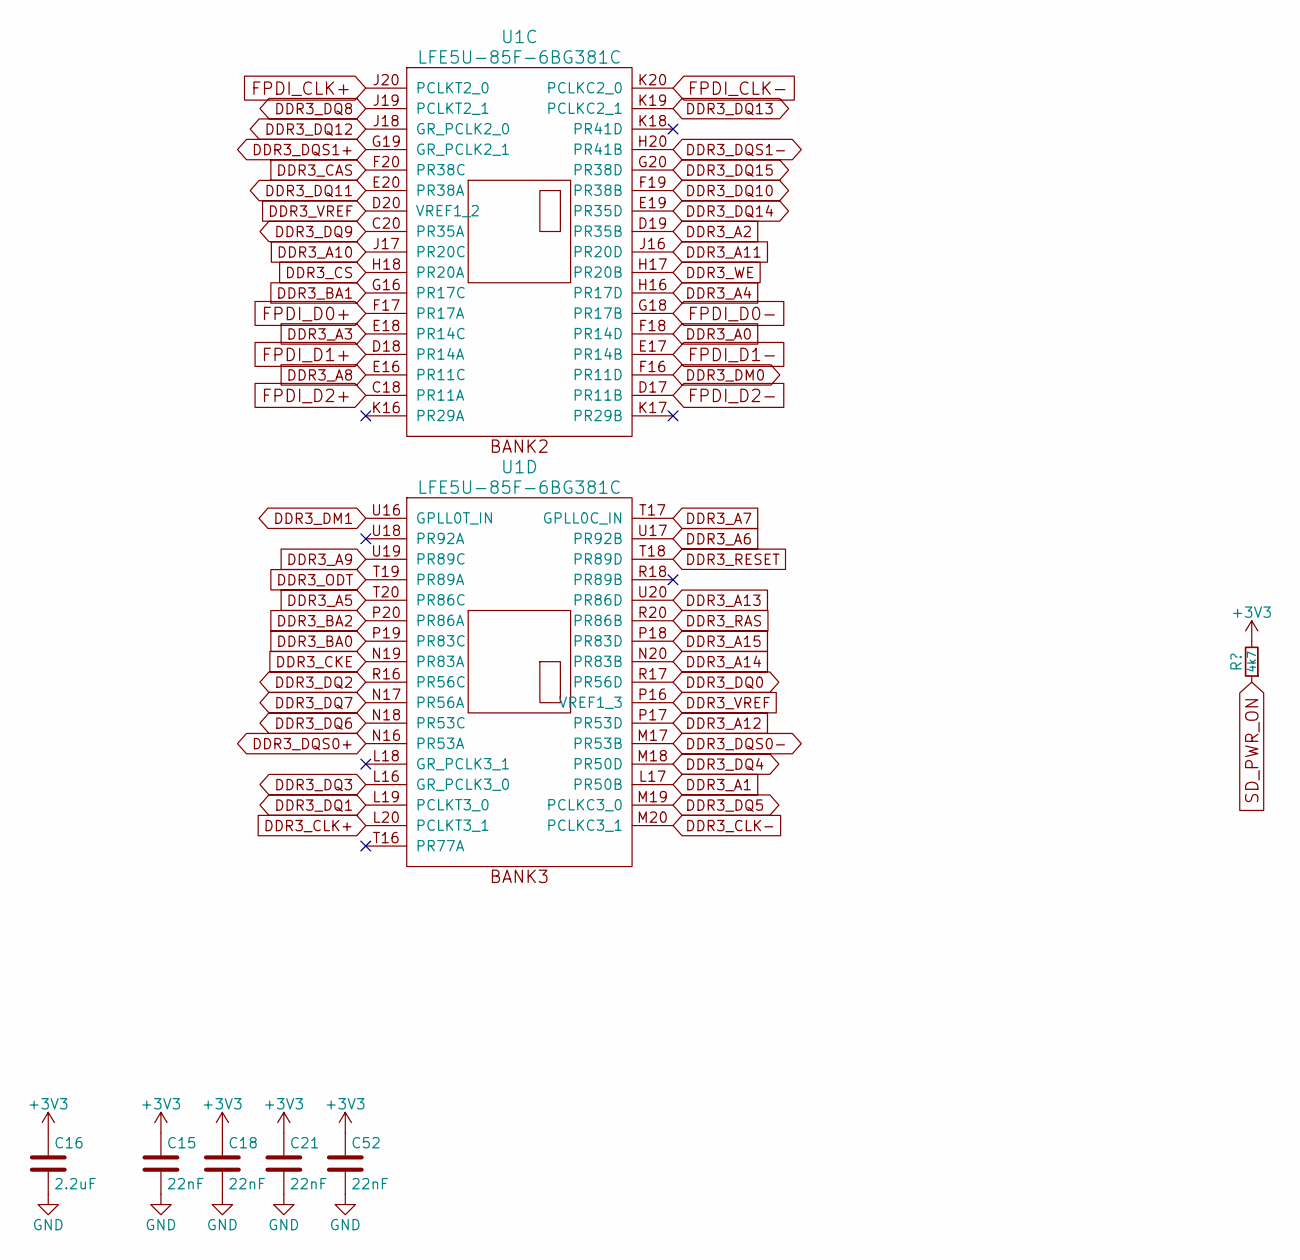
[picture p43: schematic ram.kicad_sch]

Parts:
C15, C18, C21: 22nF; C_0402_1005Metric; MPN CX0603MRX7R8BB223
C16: 2.2uF; C_0603_1608Metric
C52: 22nF; C_0603_1608Metric; MPN CX0603MRX7R8BB223
R20: 4k7; R_0402_1005Metric
U1: LFE5U-85F-6BG381C; BGA-381_pitch0.8mm_dia0.4mm; MPN LFE5U-85F-6BG381C

Connections:
+3V3: C15.1, C16.1, C18.1, C21.1, C52.1, R20.2
DDR3_A0: U1.F18 (PR14D)
DDR3_A1: U1.L17 (PR50B)
DDR3_A2: U1.D19 (PR35B)
DDR3_A3: U1.E18 (PR14C)
DDR3_A4: U1.H16 (PR17D)
DDR3_A5: U1.T20 (PR86C)
DDR3_A6: U1.U17 (PR92B)
DDR3_A7: U1.T17 (GPLL0C_IN)
DDR3_A8: U1.E16 (PR11C)
DDR3_A9: U1.U19 (PR89C)
DDR3_A10: U1.J17 (PR20C)
DDR3_A11: U1.J16 (PR20D)
DDR3_A12: U1.P17 (PR53D)
DDR3_A13: U1.U20 (PR86D)
DDR3_A14: U1.N20 (PR83B)
DDR3_A15: U1.P18 (PR83D)
DDR3_BA0: U1.P19 (PR83C)
DDR3_BA1: U1.G16 (PR17C)
DDR3_BA2: U1.P20 (PR86A)
DDR3_CAS: U1.F20 (PR38C)
DDR3_CKE: U1.N19 (PR83A)
DDR3_CLK+: U1.L20 (PCLKT3_1)
DDR3_CLK-: U1.M20 (PCLKC3_1)
DDR3_CS: U1.H18 (PR20A)
DDR3_DM0: U1.F16 (PR11D)
DDR3_DM1: U1.U16 (GPLL0T_IN)
DDR3_DQ0: U1.R17 (PR56D)
DDR3_DQ1: U1.L19 (PCLKT3_0)
DDR3_DQ2: U1.R16 (PR56C)
DDR3_DQ3: U1.L16 (GR_PCLK3_0)
DDR3_DQ4: U1.M18 (PR50D)
DDR3_DQ5: U1.M19 (PCLKC3_0)
DDR3_DQ6: U1.N18 (PR53C)
DDR3_DQ7: U1.N17 (PR56A)
DDR3_DQ8: U1.J19 (PCLKT2_1)
DDR3_DQ9: U1.C20 (PR35A)
DDR3_DQ10: U1.F19 (PR38B)
DDR3_DQ11: U1.E20 (PR38A)
DDR3_DQ12: U1.J18 (GR_PCLK2_0)
DDR3_DQ13: U1.K19 (PCLKC2_1)
DDR3_DQ14: U1.E19 (PR35D)
DDR3_DQ15: U1.G20 (PR38D)
DDR3_DQS0+: U1.N16 (PR53A)
DDR3_DQS0-: U1.M17 (PR53B)
DDR3_DQS1+: U1.G19 (GR_PCLK2_1)
DDR3_DQS1-: U1.H20 (PR41B)
DDR3_ODT: U1.T19 (PR89A)
DDR3_RAS: U1.R20 (PR86B)
DDR3_RESET: U1.T18 (PR89D)
DDR3_VREF: U1.D20 (VREF1_2), U1.P16 (VREF1_3)
DDR3_WE: U1.H17 (PR20B)
FPDI_CLK+: U1.J20 (PCLKT2_0)
FPDI_CLK-: U1.K20 (PCLKC2_0)
FPDI_D0+: U1.F17 (PR17A)
FPDI_D0-: U1.G18 (PR17B)
FPDI_D1+: U1.D18 (PR14A)
FPDI_D1-: U1.E17 (PR14B)
FPDI_D2+: U1.C18 (PR11A)
FPDI_D2-: U1.D17 (PR11B)
GND: C15.2, C16.2, C18.2, C21.2, C52.2
SD_PWR_ON: R20.1
