intergalaktik/ulx4m-ld/ulx4m-ld.kicad_sch

## KiCad design ulx4m-ld.kicad_sch (2025-04-05)

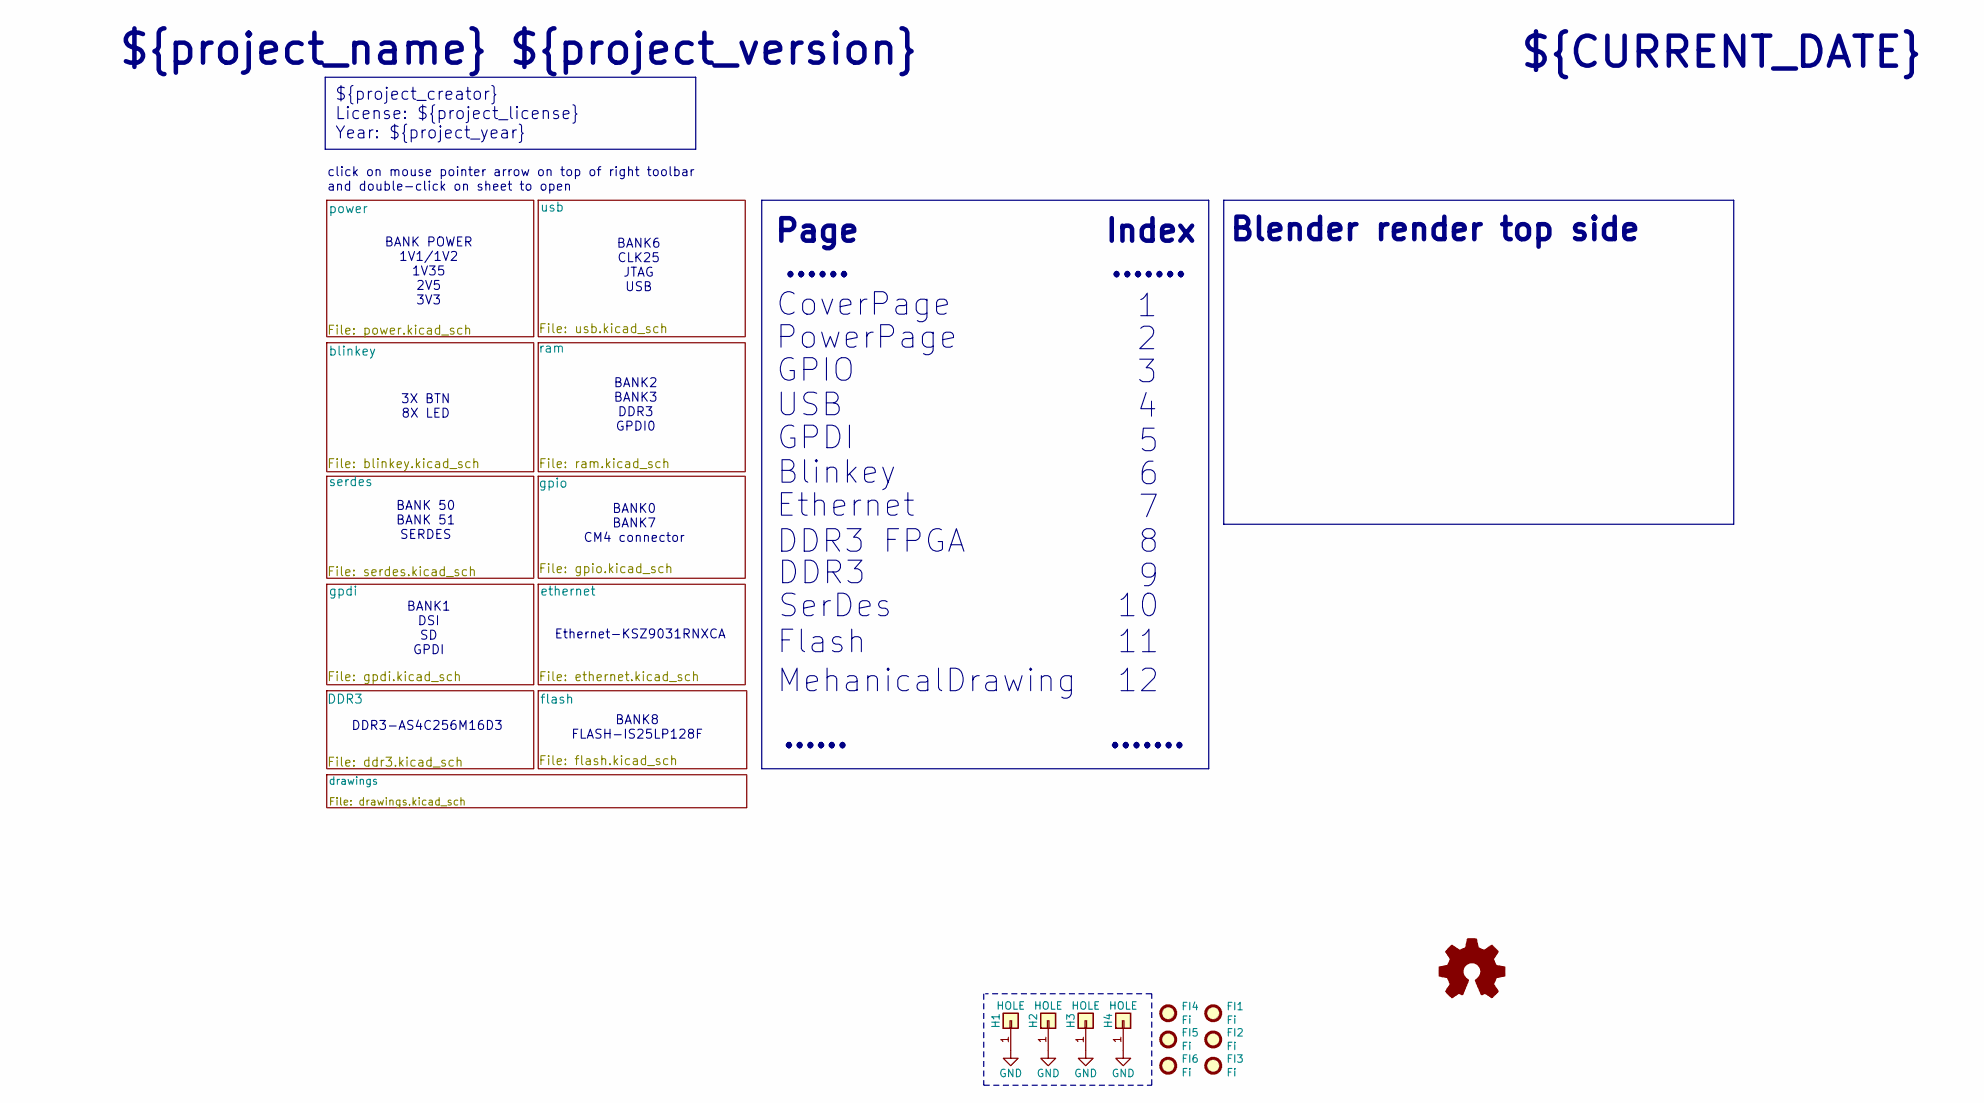
[picture p45: schematic ulx4m-ld.kicad_sch]

Parts:
FI1, FI2, FI3, FI4, FI5, FI6: Fi; Fiducial_0.5mm_Mask1mm
H1, H2, H3, H4: HOLE; MountingHole_3.2mm_M3_ISO14580_Pad

Connections:
GND: H1.1, H2.1, H3.1, H4.1

Notes on the sheet:
${project_creator} License: ${project_license} Year: ${project_year}
BANK1 DSI SD GPDI
BANK 50 BANK 51 SERDES
${project_name} ${project_version}
Flash
CoverPage
3X BTN 8X LED
Index
DDR3-AS4C256M16D3
DDR3 FPGA
Ethernet-KSZ9031RNXCA
Blender render top side
PowerPage
MehanicalDrawing
SerDes
BANK6 CLK25 JTAG USB
click on mouse pointer arrow on top of right toolbar and double-click on sheet to open
GPIO
Ethernet
.......
USB
BANK POWER 1V1/1V2 1V35 2V5 3V3
BANK8 FLASH-IS25LP128F
......
Blinkey
BANK0 BANK7 CM4 connector
Page
DDR3
BANK2 BANK3 DDR3 GPDI0
${CURRENT_DATE}
GPDI
