intergalaktik/ulx4m-ld/usb.kicad_sch

## KiCad design usb.kicad_sch (2025-04-05)

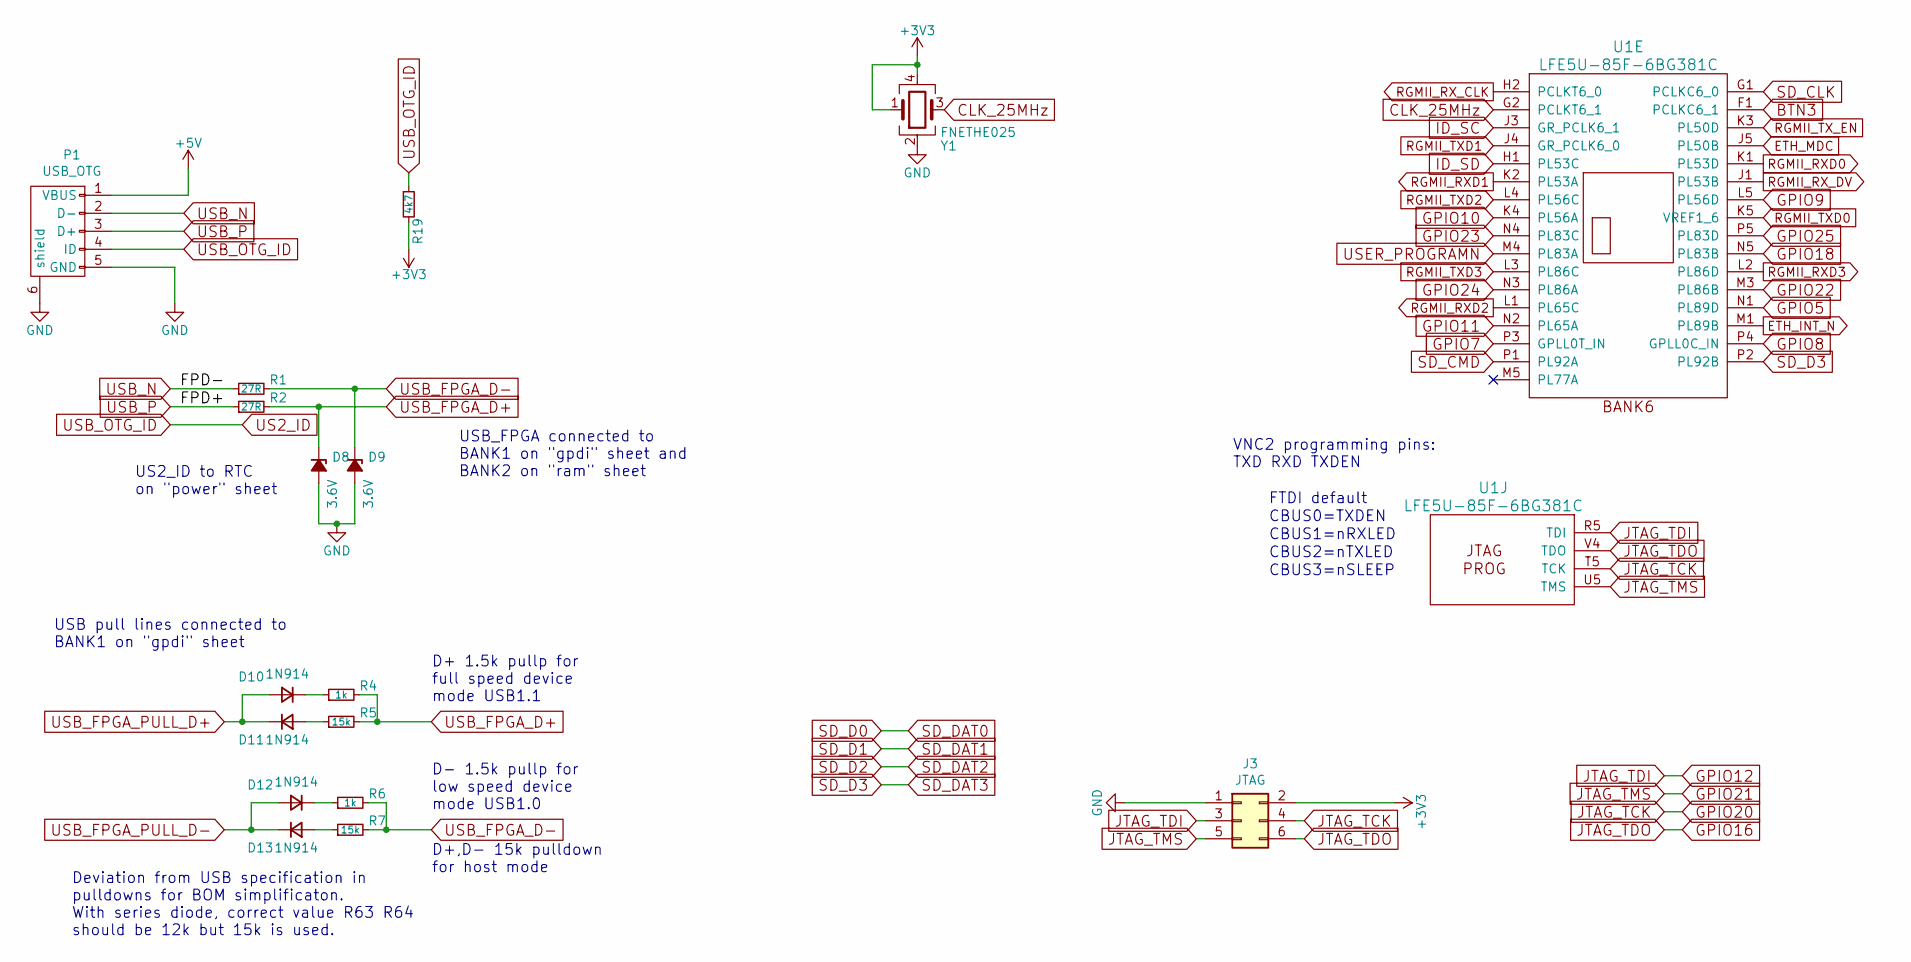
[picture p46: schematic usb.kicad_sch]

Parts:
D8, D9: 3.6V; D_SOD-323_HandSoldering; MPN BZT52C3V6S; Mouser 833-BZT52C3V6S-TP
D10, D11, D12, D13: 1N914; D_SOD-323
J3: JTAG; PinHeader_2x03_P1.00mm_Vertical_SMD
P1: USB_OTG; USB-MICRO-B-FCI-10118192-0001LF
R1, R2: 27R; R_0402_1005Metric
R4, R6: 1k; R_0402_1005Metric
R5, R7: 15k; R_0402_1005Metric
R19: 4k7; R_0402_1005Metric
U1: LFE5U-85F-6BG381C; BGA-381_pitch0.8mm_dia0.4mm; MPN LFE5U-85F-6BG381C
Y1: FNETHE025; Crystal_SMD_TXC_7M-4Pin_3.2x2.5mm; MPN FNETHE025; Mouser 729-FNETHE025

Connections:
+3V3: J3.2, R19.2, Y1.1, Y1.4
+5V: P1.1 (VBUS)
BTN3: U1.F1 (PCLKC6_1)
CLK_25MHz: U1.G2 (PCLKT6_1), Y1.3
ETH_INT_N: U1.M1 (PL89B)
ETH_MDC: U1.J5 (PL50B)
GND: D8.2 (A), D9.2 (A), J3.1, P1.5 (GND), P1.6 (shield), Y1.2
GPIO5: U1.N1 (PL89D)
GPIO7: U1.P3 (GPLL0T_IN)
GPIO8: U1.P4 (GPLL0C_IN)
GPIO9: U1.L5 (PL56D)
GPIO10: U1.K4 (PL56A)
GPIO11: U1.N2 (PL65A)
GPIO12: J3.3, U1.R5 (TDI)
GPIO16: J3.6, U1.V4 (TDO)
GPIO18: U1.N5 (PL83B)
GPIO20: J3.4, U1.T5 (TCK)
GPIO21: J3.5, U1.U5 (TMS)
GPIO22: U1.M3 (PL86B)
GPIO23: U1.N4 (PL83C)
GPIO24: U1.N3 (PL86A)
GPIO25: U1.P5 (PL83D)
ID_SC: U1.J3 (GR_PCLK6_1)
ID_SD: U1.H1 (PL53C)
unnamed: D10.1 (K), R4.1
unnamed: D11.2 (A), R5.1
unnamed: D12.1 (K), R6.1
unnamed: D13.2 (A), R7.1
RGMII_RXD0: U1.K1 (PL53D)
RGMII_RXD1: U1.K2 (PL53A)
RGMII_RXD2: U1.L1 (PL65C)
RGMII_RXD3: U1.L2 (PL86D)
RGMII_RX_CLK: U1.H2 (PCLKT6_0)
RGMII_RX_DV: U1.J1 (PL53B)
RGMII_TXD0: U1.K5 (VREF1_6)
RGMII_TXD1: U1.J4 (GR_PCLK6_0)
RGMII_TXD2: U1.L4 (PL56C)
RGMII_TXD3: U1.L3 (PL86C)
RGMII_TX_EN: U1.K3 (PL50D)
SD_CLK: U1.G1 (PCLKC6_0)
SD_CMD: U1.P1 (PL92A)
SD_D3: U1.P2 (PL92B)
US2_ID: P1.4 (ID), R19.1
USB_FPGA_D+: D8.1 (K), R2.2, R4.2, R5.2
USB_FPGA_D-: D9.1 (K), R1.2, R6.2, R7.2
USB_FPGA_PULL_D+: D10.2 (A), D11.1 (K)
USB_FPGA_PULL_D-: D12.2 (A), D13.1 (K)
USB_N: P1.2 (D-), R1.1
USB_P: P1.3 (D+), R2.1
USER_PROGRAMN: U1.M4 (PL83A)

Notes on the sheet:
D+,D- 15k pulldown for host mode
D- 1.5k pullp for low speed device mode USB1.0
CBUS3=nSLEEP
CBUS0=TXDEN
FTDI default
Deviation from USB specification in pulldowns for BOM simplificaton. With series diode, correct value R63 R64 should be 12k but 15k is used.
CBUS1=nRXLED
US2_ID to RTC on "power" sheet
CBUS2=nTXLED
USB_FPGA connected to BANK1 on "gpdi" sheet and BANK2 on "ram" sheet
D+ 1.5k pullp for full speed device mode USB1.1
VNC2 programming pins: TXD RXD TXDEN
USB pull lines connected to BANK1 on "gpdi" sheet
